Blinkinlabs/EightByEight/firmware/serialloop.cpp

/*
 * Simple serial protocol handler
 *
 * Copyright (c) 2014, 2016 Blinkinlabs, LLC
 *
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
 * THE SOFTWARE IS PROVIDED "AS IS", WITHOUT WARRANTY OF ANY KIND, EXPRESS OR
 * IMPLIED, INCLUDING BUT NOT LIMITED TO THE WARRANTIES OF MERCHANTABILITY, FITNESS
 * FOR A PARTICULAR PURPOSE AND NONINFRINGEMENT. IN NO EVENT SHALL THE AUTHORS OR
 * COPYRIGHT HOLDERS BE LIABLE FOR ANY CLAIM, DAMAGES OR OTHER LIABILITY, WHETHER
 * IN AN ACTION OF CONTRACT, TORT OR OTHERWISE, ARISING FROM, OUT OF OR IN
 * CONNECTION WITH THE SOFTWARE OR THE USE OR OTHER DEALINGS IN THE SOFTWARE.
 */

#include "eightbyeight.h"
#include "serialloop.h"
#include "HardwareSerial.h"
#include "matrix.h"

#include <stdlib.h>

#define SERIAL_MODE_DATA     0x01
#define SERIAL_MODE_COMMAND  0x02

// We start in BlinkyTape mode, but if we get the magic escape sequence, we transition
// to BlinkyTile mode.
// Escape sequence is 10 0xFF characters in a row.

int serialMode;         // Serial protocol we are speaking

///// Defines for the data mode
void dataLoop();

int escapeRunCount;     // Count of how many escape characters we've received
uint8_t buffer[3];      // Buffer for one pixel of data
int bufferIndex;        // Current location in the buffer
int pixelIndex;         // Pixel we are currently writing to

///// Defines for the control mode
void commandLoop();

#define CONTROL_BUFFER_SIZE 100
uint8_t controlBuffer[CONTROL_BUFFER_SIZE];     // Buffer for receiving command data
int controlBufferIndex;     // Current location in the buffer

void serialReset() {
    serialMode = SERIAL_MODE_DATA;

    bufferIndex = 0;
    pixelIndex = 0;

    escapeRunCount = 0;

    controlBufferIndex = 0;
}

void serialLoop() {
    switch(serialMode) {
        case SERIAL_MODE_DATA:
            dataLoop();
            break;
        case SERIAL_MODE_COMMAND:
            commandLoop();
            break;
        default:
            serialReset();
    }
}

void dataLoop() {
    uint8_t c = serial2_getchar();

    // Pixel character
    if(c != 0xFF) {
        // Reset the control character state variables
        escapeRunCount = 0;

        // Buffer the color
        buffer[bufferIndex++] = c;

        // If this makes a complete pixel color, update the display and reset for the next color
        if(bufferIndex > 2) {
            bufferIndex = 0;

            // Prevent overflow by ignoring any pixel data beyond LED_COUNT
            if(pixelIndex < LED_COUNT) {
                matrix.setPixelColor(pixelIndex%LED_COLS, pixelIndex/LED_COLS,
                         buffer[0], buffer[1], buffer[2]);
                pixelIndex++;
            }
        }
    }

    // Control character
    else {
        // reset the pixel character state vairables
        bufferIndex = 0;
        pixelIndex = 0;

        escapeRunCount++;

        // If this is the first escape character, refresh the output
        if(escapeRunCount == 1) {
            //memcpy(getPixels(), frameData, LED_ROWS*LED_COLS*BYTES_PER_PIXEL);
            matrix.show();
        }
        
        if(escapeRunCount > 8) {
            serialMode = SERIAL_MODE_COMMAND;
            controlBufferIndex = 0;
        }
    }
}

bool commandSetBrightness(uint8_t* buffer);

struct Command {
    uint8_t name;   // Command identifier
    int length;     // Command length (number of bytes to read)
    bool (*function)(uint8_t*);
};

Command commands[] = {
    {0x01,   2,   commandSetBrightness},  // Set the display brightness
//    {0x02,   65,  commandWrite},        // Write 64 bytes of data
//    {0x03,   1,   commandStopWrite},    // Stop writing
//    {0x04,   1,   commandStartRead},    // Start reading back the animation
//    {0x05,   1,   commandRead},         // Read 64 bytes of data
//    {0x06,   1,   commandStopRead},     // Stop reading
    {0xFF,   0,   NULL}
};


void commandLoop() {
    uint8_t c = serial2_getchar();

    // If we get extra 0xFF bytes before the command byte, ignore them
    if((controlBufferIndex == 0) && (c == 0xFF))
        return;

    controlBuffer[controlBufferIndex++] = c;

    for(Command *command = commands; 1; command++) {
        // If the command isn't found in the list, bail
        if(command->name == 0xFF) {
            serialReset();
            break;
        }

        // If this iteration isn't the correct one, keep looking
        if(command->name != controlBuffer[0])
            continue;

        // Now we're on to something- have we gotten enough data though?
        if(controlBufferIndex >= command->length) {
            if(command->function(controlBuffer + 1)) {
                serial2_putchar('P');
                serial2_putchar((char)controlBuffer[1]);
                serial2_write(controlBuffer + 2, controlBuffer[1] + 1);
            }
            else {
                serial2_putchar('F');
                serial2_putchar((char)controlBuffer[1]);
                serial2_write(controlBuffer + 2, controlBuffer[1] + 1);
            }

            serialReset();
        }
        break;
    }
}

// Brightness, 0-255
bool commandSetBrightness(uint8_t* buffer) {
    matrix.setBrightness(buffer[0]/255.0);

    buffer[0] = 0;
    return true;
}
