Blinkinlabs/EightByEight/examples/PlayerMode/PlayerMode.ino

// Upload settings:
// -Generic ESP8266 Module
// -Upload Speed: 460800
// -CPU Frequency: 80MHz
// -Flash Frequency: 40MHz
// -Flash Mode: QIO (fast)
// -Flash Size: 2M (1M SPIFFS)
// -Crystal Frequency: 26MHz
// -Reset Method: nodemcu
// 

/** \file
 * Combine multiple demos for the Two Sigma / Blinklabs EightByEight badge.
 *
 * The button is used to cycle between the different demos.
 *
 * Pixels and SerialReceiver are not really seperate demos; we switch to them
 * automatically if they tell us that they have received a packet.
 * If we go more than ten seconds without a packet, the current demo
 * is restarted.
 */

#include "FS.h"

#include "Badge.h"
#include "Pixels.h"
#include "SerialReceiver.h"
#include "patterns.h"
#include "patterndemo.h"

#include "Life.h"
#include "Bubble.h"
#include "Rain.h"
#include "ColorSwirl.h"

Badge badge;

volatile bool fileAccessLocked;
volatile bool reloadAnimations;

Pixels pixels; // udp packet receiver
SerialReceiver serialReceiver;  // BlinkyTape communications protocol

Patterns patterns;

PatternDemo patternDemo;

Bubble bubble;  // Enabled demos
Life life;
Rain rain;
ColorSwirl colorSwirl;

Demo * builtin_demos[] = {
//    &rain,
//    &life,
//    &bubble,
//    &colorSwirl
};

const unsigned builtin_demo_count = sizeof(builtin_demos)/sizeof(Demo *);
unsigned demo_num = 0;
Demo * demo;

uint32_t last_draw_millis;
uint32_t streaming_start_time;
bool streaming;

void load_demo(unsigned new_demo_num)
{
    // The demo order is:
    // 0 to (n-1): stored patterns, where n is the number of stored patterns
    // (n-1) to (n-1+builtin_demo_count): built-in demos

    unsigned int total_demos = patterns.getCount() + builtin_demo_count;

    Serial.print("demo count:");
    Serial.println(total_demos);

    if(total_demos == 0) {
      demo_num = 0;
      demo = nullptr;
      return;
    }

    if(new_demo_num > total_demos) {
      new_demo_num = 0;
    }

    if(new_demo_num < patterns.getCount()) {
        // TODO: If this fails, load a built-in pattern?
        patternDemo = patterns.open(new_demo_num);
        demo = &patternDemo;
    }
    else {
        demo = builtin_demos[new_demo_num - patterns.getCount()];
    }

    demo_num = new_demo_num;
}


void setup()
{
    badge.begin();

    WiFi.persistent(false);

    SPIFFS.begin();
//    SPIFFS.format();

    // do not join any wifi networks if the button is held down
    // during startup
    /*
    if (!badge.button())
    {
#if 0
        WiFi.mode(WIFI_STA);
        WiFi.begin("twosigma-blinky", "blinkblinkblink");
#else
        WiFi.mode(WIFI_AP);
        WiFi.begin("ssid", "password");
        WiFi.config(IPAddress(192,168,1,4), IPAddress(0,0,0,0), IPAddress(255,255,255,0));
#endif
    }
    */

    pixels.begin();

    serialReceiver.begin();

    fileAccessLocked = false;
    reloadAnimations = true;

    // Initialize all of the demos and start at 0
    for(int i = 0 ; i < builtin_demo_count ; i++)
        builtin_demos[i]->begin();

    load_demo(0);
}

void loop()
{
    if(reloadAnimations) {
        patterns.begin();
        reloadAnimations = false;

        load_demo(0);
    }

    if (badge.poll())
    {
        if(demo != nullptr)
          demo->tapped();
    }

//    if (badge.button_edge())
//    {
//        load_demo(demo_num + 1);
//    }

    const uint32_t now = millis();

    bool do_draw = false;
    
    if(demo != nullptr)
      demo->step(badge.ax, badge.ay, badge.az);

    if (serialReceiver.step(0,0,0))
    {
        streaming = true;
        streaming_start_time = now;

        serialReceiver.draw(badge.matrix);
        badge.matrix.show();
    }

    if (pixels.step(0,0,0))
    {
        streaming = true;
        streaming_start_time = now;

        pixels.draw(badge.matrix);
        badge.matrix.show();
    }


    if (streaming && (now - streaming_start_time > 10000ul))
    {
        // no video for ten seconds, go back to normal demo
        streaming = false;
    }

    if (!streaming)
    {
        // Draw the LEDs at 60Hz
        if (!do_draw && now - last_draw_millis < (1000/60))
            return;

        last_draw_millis = now;

        if(demo != nullptr) {
          demo->draw(badge.matrix);
        }
        else {
          // Clear the display, but draw a blue corner
          badge.matrix.clear();
          badge.matrix.set(0,0,0,0,255);
          badge.matrix.set(7,0,255,0,0);
          badge.matrix.set(0,7,0,255,0);
          badge.matrix.set(7,7,255,255,255);
        }
          
        badge.matrix.show();
    }

    if(demo != nullptr) {
      if(demo->done())
        load_demo(demo_num + 1);
    }
}
